Somebud0180/Ctrl_pad/QMK/Ctrl_pad/keymaps/default/keymap.c

// Copyright 2023 QMK
// SPDX-License-Identifier: GPL-2.0-or-later

#include QMK_KEYBOARD_H
#define ENCODER_MAP_KEY_DELAY 10
#define ANIMATION_FRAME_DELAY 200

// Define the layers
enum layer_names {
    _BL,
    _SL,
};

// Keymaps
const uint16_t PROGMEM keymaps[][MATRIX_ROWS][MATRIX_COLS] = {
    /*
     * ┌─────┬─────┬─────┐
     * │ F13 │ F14 │ F15 │
     * ├─────┼─────┼─────┤
     * │ F16 │ F17 │ F18 │
     * ├─────┼─────┼─────┤
     * │ F19 │ F20 │ F21 │
     * └─────┴─────┴─────┘
     */
    [_BL] = LAYOUT( 
        KC_SLEP,        KC_WAKE,        TO(_SL),
        KC_MPRV,        KC_MPLY,        KC_MNXT, 
        LGUI(KC_C),     LGUI(KC_X),     LGUI(KC_V)
        ),

    [_SL] = LAYOUT( 
        KC_F1,      KC_F2,      TO(_BL),  
        KC_F3,      KC_F4,      KC_F5,
        KC_F6,      KC_F7,      KC_F8
        ),
};

// Shared variables
bool animation_in_progress = false;
uint32_t animation_timer = 0;
int8_t encoder_state = 0;
uint8_t frame_index = 0;
uint8_t prev_layer = 0;

// Function prototypes
static void render_animation(void);

// Encoder Function
bool encoder_update_user(uint8_t index, bool clockwise) {
    if (index == 0) { /* First encoder */
        oled_on();
        if (clockwise) {
            if (get_highest_layer(layer_state) == _BL) {
                tap_code(0x80);
                animation_in_progress = true;
                encoder_state = 1;
                animation_timer = timer_read();
                frame_index = 0;
            } else {
                tap_code(KC_BRIGHTNESS_UP);
                animation_in_progress = true;
                encoder_state = 1;
                animation_timer = timer_read();
                frame_index = 0;
            }
        } else {
            if (get_highest_layer(layer_state) == _BL) {
                tap_code(0x81);
                animation_in_progress = true;
                encoder_state = -1;
                animation_timer = timer_read();
                frame_index = 3;
            } else {
                tap_code(KC_BRIGHTNESS_DOWN);
                animation_in_progress = true;
                encoder_state = -1;
                animation_timer = timer_read();
                frame_index = 3;
            }
        } 
    }
    return false;
}

// Animation Bitmaps

// Volume Bitmaps
// 'Vol0', 128x48px
static const char epd_bitmap_Vol0[] PROGMEM = {0x00, 0x00, 0x00, 0x00, 0x00, 0x00, 0x00, 0x00, 0x00, 0x00, 0x00, 0x00, 0x00, 0x00, 0x00, 0x00, 0x00, 0x00, 0x00, 0x00, 0x00, 0x00, 0x00, 0x00, 0x00, 0x00, 0x00, 0x00, 0x00, 0x00, 0x00, 0x00, 0x00, 0x00, 0x00, 0x00, 0x00, 0x00, 0x00, 0x00, 0x00, 0x00, 0x00, 0x00, 0x00, 0x00, 0x00, 0x00, 0x00, 0x00, 0x00, 0x00, 0x00, 0x00, 0x00, 0x00, 0x00, 0x00, 0x00, 0x00, 0x00, 0x00, 0x00, 0x00, 0x00, 0x00, 0x00, 0x00, 0x00, 0x00, 0x00, 0x00, 0x00, 0x00, 0x00, 0x00, 0x00, 0x00, 0x00, 0x00, 0x00, 0x00, 0x00, 0x00, 0x00, 0x00, 0x00, 0x00, 0x00, 0x00, 0x00, 0x00, 0x00, 0x00, 0x00, 0x00, 0x00, 0x00, 0x00, 0x00, 0x00, 0x00, 0x00, 0x00, 0x00, 0x00, 0x00, 0x00, 0x00, 0x00, 0x00, 0x00, 0x00, 0x00, 0x00, 0x00, 0x00, 0x00, 0x00, 0x00, 0x00, 0x00, 0x00, 0x00, 0x00, 0x00, 0x00, 0x00, 0x00, 0x00, 0x00, 0x00, 0x00, 0x00, 0x00, 0x00, 0x00, 0x00, 0x00, 0x00, 0x00, 0x00, 0x00, 0x00, 0x00, 0x00, 0x00, 0x00, 0x00, 0x00, 0x00, 0x00, 0x00, 0x00,
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
uint16_t sun_frame_sizes[4] = {sizeof(epd_bitmap_Sun0), sizeof(epd_bitmap_Sun1), sizeof(epd_bitmap_Sun2), sizeof(epd_bitmap_Sun3)};

// OLED Function
#ifdef OLED_ENABLE

static void render_animation(void) {
    uint8_t current_layer = get_highest_layer(layer_state);

    // Check if layer changed during animation
    if (current_layer != prev_layer) {
        // Reset animation state for new layer
        frame_index = 3;
        animation_in_progress = false;
        prev_layer = current_layer;
    }    

    // Run Animation
    if (IS_LAYER_ON(_BL)) {
        oled_write_raw_P(epd_bitmap_allVolArray[frame_index], vol_frame_sizes[frame_index]);
    } else if (IS_LAYER_ON(_SL)) {
        oled_write_raw_P(epd_bitmap_allSunArray[frame_index], sun_frame_sizes[frame_index]);
    }

    // Update the frame index based on timing
    if (timer_elapsed(animation_timer) > ANIMATION_FRAME_DELAY && animation_in_progress) {
        animation_timer = timer_read();
        
        if (encoder_state == 1) { // Forward animation
            frame_index++;
            if (frame_index >= 4) {
                animation_in_progress = false;
            }
        } else if (encoder_state == -1) { // Backward animation
            if (frame_index == 0) {
                animation_in_progress = false;
            } else {
                frame_index--;
            }
        }
    }
}

bool oled_task_user(void) {
    static bool oled_initialized = false;
    uint8_t current_layer = get_highest_layer(layer_state);

    // Initialize OLED display once
    if (!oled_initialized) {
        oled_clear();
        prev_layer = current_layer;
        oled_initialized = true;
    }

    // Display the layer info at the top
    oled_set_cursor(0, 0);
    switch (get_highest_layer(layer_state)) {
        case _BL:
            oled_write_ln_P(PSTR("Layer: Ctrl"), false);
            break;
        case _SL:
            oled_write_ln_P(PSTR("Layer: Func"), false);
            break;
        default:
            oled_write_ln_P(PSTR("Layer: Undefined"), false);
            break;
    }

    // Display encoder functionality
    oled_set_cursor(0, 1);
    if (IS_LAYER_ON(_BL)) {
        oled_write_ln_P(PSTR("Vol Ctrl"), false);
    } else if (IS_LAYER_ON(_SL)) {
        oled_write_ln_P(PSTR("Bright Ctrl"), false);
    }

    // Handle layer change even when not animating
    if (current_layer != prev_layer && !animation_in_progress) {
        prev_layer = current_layer;
    }

    // Render the animation below the layer info
    if (animation_in_progress) {
        render_animation();
    } else {
        // Display static image based on current layer
        if (IS_LAYER_ON(_BL)) {
            oled_write_raw_P(epd_bitmap_allVolArray[3], vol_frame_sizes[3]);
        } else if (IS_LAYER_ON(_SL)) {
            oled_write_raw_P(epd_bitmap_allSunArray[3], sun_frame_sizes[3]);
        }
    }

    return false;
}

#endif // OLED_ENABLE
